KernelPanicGR/Arduino-UV_Box-7-Segment-Display-Countdown-Timer/Photos/Arduino_Countdown_Timer_7seg07.jpg

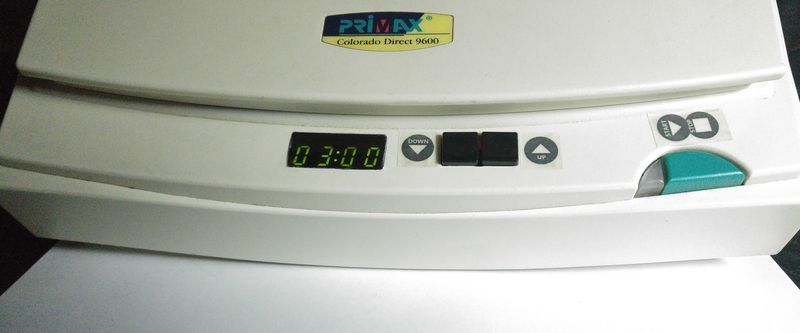
Photos/Arduino_Countdown_Timer_7seg07.jpg
